dilshan/musical-plants/firmware/musical-plant-usb.c

//****************************************************************************
// Musical Plants - PIC18F4550 Firmware (Version 1.0)
// Designed for CoCA Emerge + Tech project.
//
// Copyright (c) 2016 Dilshan R Jayakody [jayakody2000lk at gmail dot com].
//
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
const unsigned int USB_VENDOR_ID = 0x1984;
const unsigned int USB_PRODUCT_ID = 0x0015;
const char USB_SELF_POWER = 0xC0;            
const char USB_MAX_POWER = 50;
const char HID_INPUT_REPORT_BYTES = 64;
const char HID_OUTPUT_REPORT_BYTES = 64;
const char USB_TRANSFER_TYPE = 0x03;
const char EP_IN_INTERVAL = 1;
const char EP_OUT_INTERVAL = 1;

const char USB_INTERRUPT = 1;
const char USB_HID_EP = 1;
const char USB_HID_RPT_SIZE = 33;

// Device descriptor.
const struct 
{
    char bLength;           
    char bDescriptorType;   
    unsigned int bcdUSB;    
    char bDeviceClass;      
    char bDeviceSubClass;   
    char bDeviceProtocol;   
    char bMaxPacketSize0;   
    unsigned int idVendor;  
    unsigned int idProduct; 
    unsigned int bcdDevice; 
    char iManufacturer;     
    char iProduct;          
    char iSerialNumber;     
    char bNumConfigurations;
} 
device_dsc = 
{
    0x12,          
	0x01,          
	0x0200,        
	0x00,          
	0x00,          
	0x00,          
	8,             
	USB_VENDOR_ID, 
	USB_PRODUCT_ID,
	0x0001,        
	0x01,          
	0x02,          
	0x00,          
	0x01           
};

// Configuration descriptor.
const char configDescriptor1[]= 
{
    0x09,                  
    0x02,                  
    0x29,0x00,             
    1,                     
    1,                     
    0,                     
    USB_SELF_POWER,        
    USB_MAX_POWER,         
    0x09,                  
    0x04,                  
    0,                     
    0,                     
    2,                     
    0x03,                  
    0,                     
    0,                     
    0,                     
    0x09,                 
    0x21,                 
    0x01,0x01,            
    0x00,                 
    1,                    
    0x22,                 
    USB_HID_RPT_SIZE,0x00,
    0x07,             
    0x05,             
    USB_HID_EP | 0x80,
    USB_TRANSFER_TYPE,
    0x40,0x00,        
    EP_IN_INTERVAL,   
    0x07,             
    0x05,             
    USB_HID_EP,       
    USB_TRANSFER_TYPE,
    0x40,0x00,        
    EP_OUT_INTERVAL   
};

const struct 
{
    char report[USB_HID_RPT_SIZE];
}
hid_rpt_desc =
{
   {
	  0x06, 0x00, 0xFF,       
      0x09, 0x01,             
      0xA1, 0x01,             
      0x19, 0x01,             
      0x29, 0x40,             
      0x15, 0x00,             
      0x26, 0xFF, 0x00,       
      0x75, 0x08,             
      0x95, HID_INPUT_REPORT_BYTES,
      0x81, 0x02,
      0x19, 0x01,
      0x29, 0x40,
      0x75, 0x08,
      0x95, HID_OUTPUT_REPORT_BYTES,
      0x91, 0x02,
      0xC0
   }
};

const struct 
{
	char bLength;
	char bDscType;
	unsigned int string[1];
} 
strd1 = 
{
	4,
	0x03,
	{
		0x0409
	}
};


// Manufacturer string descriptor.
const struct
{
  char bLength;
  char bDscType;
  unsigned int string[18];
}
strd2=
{
    38,
    0x03,
    {
		'D','i','l','s','h','a','n',' ','R',' ','J','a','y','a','k','o','d','y'
	}
};

// Product string descriptor.
const struct
{
  char bLength;
  char bDscType;
  unsigned int string[25];
}
strd3=
{
    52,
    0x03,
    {
		'M','u','s','i','c','a','l',' ','P','l','a','n','t','s',' ','S','e','n','s','o','r',' ','K','i','t'
	}
};

//Array of configuration descriptors.
const char* USB_config_dsc_ptr[1];

//Array of string descriptors.
const char* USB_string_dsc_ptr[3];

void USB_Init_Desc()
{
  USB_config_dsc_ptr[0] = &configDescriptor1;
  USB_string_dsc_ptr[0] = (const char*)&strd1;
  USB_string_dsc_ptr[1] = (const char*)&strd2;
  USB_string_dsc_ptr[2] = (const char*)&strd3;
}
